yopocho/ChristmasMantelClock/src/ui/ui_font_courier_new_16.c

/*******************************************************************************
 * Size: 16 px
 * Bpp: 1
 * Opts: --bpp 1 --size 16 --no-compress --font ..\..\Downloads\cour.ttf --symbols abcdefghijklmnopqrstuvwxyzABCDEFGHIJKLMNOPQRSTUVWXYZ0123456789:_-+"?!@#$%^&*()[]˅˯ --format lvgl
 ******************************************************************************/

#ifdef __has_include
    #if __has_include("lvgl.h")
        #ifndef LV_LVGL_H_INCLUDE_SIMPLE
            #define LV_LVGL_H_INCLUDE_SIMPLE
        #endif
    #endif
#endif

#ifdef LV_LVGL_H_INCLUDE_SIMPLE
    #include "lvgl.h"
#else
    #include "lvgl.h"
#endif

#ifndef UI_FONT_COURIER_NEW_16
#define UI_FONT_COURIER_NEW_16 1
#endif

#if UI_FONT_COURIER_NEW_16

/*-----------------
 *    BITMAPS
 *----------------*/

/*Store the image of the glyphs*/
static LV_ATTRIBUTE_LARGE_CONST const uint8_t glyph_bitmap[] = {
    /* U+0020 " " */
    0x0,

    /* U+0021 "!" */
    0xaa, 0xa0, 0x30,

    /* U+0022 "\"" */
    0xcb, 0x2c, 0x92,

    /* U+0023 "#" */
    0x28, 0x50, 0xa1, 0x47, 0xe5, 0xa, 0x7f, 0x28,
    0x50, 0xa1, 0x40,

    /* U+0024 "$" */
    0x10, 0x79, 0x92, 0x4, 0x7, 0x1, 0xc1, 0xc6,
    0x78, 0x40, 0x80,

    /* U+0025 "%" */
    0x30, 0x91, 0x21, 0x80, 0x67, 0x13, 0x9, 0x12,
    0x18,

    /* U+0026 "&" */
    0x39, 0x4, 0x10, 0x23, 0x59, 0x62, 0x74,

    /* U+0028 "(" */
    0x29, 0x49, 0x24, 0x89, 0x10,

    /* U+0029 ")" */
    0x89, 0x12, 0x49, 0x29, 0x40,

    /* U+002A "*" */
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
    0x42, 0xe7,

    /* U+0069 "i" */
    0x10, 0x0, 0x3, 0x81, 0x2, 0x4, 0x8, 0x11,
    0xfc,

    /* U+006A "j" */
    0x10, 0x1, 0xf0, 0x84, 0x21, 0x8, 0x42, 0x3f,
    0x0,

    /* U+006B "k" */
    0xc0, 0x40, 0x40, 0x4e, 0x48, 0x50, 0x70, 0x48,
    0x44, 0xc7,

    /* U+006C "l" */
    0x70, 0x20, 0x40, 0x81, 0x2, 0x4, 0x8, 0x11,
    0xfc,

    /* U+006D "m" */
    0xf7, 0x24, 0x92, 0x49, 0x24, 0x92, 0x4b, 0xb6,

    /* U+006E "n" */
    0xdc, 0x62, 0x42, 0x42, 0x42, 0x42, 0xe7,

    /* U+006F "o" */
    0x3c, 0x42, 0x81, 0x81, 0x81, 0x42, 0x3c,

    /* U+0070 "p" */
    0xdc, 0x62, 0x41, 0x41, 0x41, 0x62, 0x5c, 0x40,
    0x40, 0xf0,

    /* U+0071 "q" */
    0x3b, 0x46, 0x82, 0x82, 0x82, 0x46, 0x3a, 0x2,
    0x2, 0xf,

    /* U+0072 "r" */
    0xe6, 0x38, 0x20, 0x20, 0x20, 0x20, 0xfc,

    /* U+0073 "s" */
    0x3c, 0x89, 0x1, 0xe0, 0x30, 0xff, 0x0,

    /* U+0074 "t" */
    0x20, 0x20, 0xfe, 0x20, 0x20, 0x20, 0x20, 0x21,
    0x1e,

    /* U+0075 "u" */
    0xce, 0x42, 0x42, 0x42, 0x42, 0x46, 0x3b,

    /* U+0076 "v" */
    0xf3, 0x90, 0x88, 0x84, 0x41, 0x20, 0xa0, 0x30,

    /* U+0077 "w" */
    0xe3, 0xa0, 0x92, 0x49, 0xa3, 0x51, 0xb0, 0xc8,

    /* U+0078 "x" */
    0xe6, 0x44, 0x28, 0x10, 0x2c, 0x42, 0xe7,

    /* U+0079 "y" */
    0xe3, 0x42, 0x42, 0x24, 0x24, 0x18, 0x8, 0x10,
    0x10, 0xf8,

    /* U+007A "z" */
    0xfe, 0x21, 0x8, 0x41, 0x1f, 0xc0,

    /* U+02C5 "˅" */
    0x81, 0x82, 0x42, 0x44, 0x24, 0x18, 0x18, 0x0,

    /* U+02EF "˯" */
    0xa8
};


/*---------------------
 *  GLYPH DESCRIPTION
 *--------------------*/

static const lv_font_fmt_txt_glyph_dsc_t glyph_dsc[] = {
    {.bitmap_index = 0, .adv_w = 0, .box_w = 0, .box_h = 0, .ofs_x = 0, .ofs_y = 0} /* id = 0 reserved */,
    {.bitmap_index = 0, .adv_w = 154, .box_w = 1, .box_h = 1, .ofs_x = 0, .ofs_y = 0},
    {.bitmap_index = 1, .adv_w = 154, .box_w = 2, .box_h = 10, .ofs_x = 4, .ofs_y = 0},
    {.bitmap_index = 4, .adv_w = 154, .box_w = 6, .box_h = 4, .ofs_x = 2, .ofs_y = 6},
    {.bitmap_index = 7, .adv_w = 154, .box_w = 7, .box_h = 12, .ofs_x = 1, .ofs_y = -1},
    {.bitmap_index = 18, .adv_w = 154, .box_w = 7, .box_h = 12, .ofs_x = 1, .ofs_y = -2},
    {.bitmap_index = 29, .adv_w = 154, .box_w = 7, .box_h = 10, .ofs_x = 1, .ofs_y = 0},
    {.bitmap_index = 38, .adv_w = 154, .box_w = 6, .box_h = 9, .ofs_x = 2, .ofs_y = 0},
    {.bitmap_index = 45, .adv_w = 154, .box_w = 3, .box_h = 12, .ofs_x = 5, .ofs_y = -2},
    {.bitmap_index = 50, .adv_w = 154, .box_w = 3, .box_h = 12, .ofs_x = 2, .ofs_y = -2},
    {.bitmap_index = 55, .adv_w = 154, .box_w = 7, .box_h = 6, .ofs_x = 1, .ofs_y = 4},
    {.bitmap_index = 61, .adv_w = 154, .box_w = 7, .box_h = 9, .ofs_x = 1, .ofs_y = 0},
    {.bitmap_index = 69, .adv_w = 154, .box_w = 7, .box_h = 1, .ofs_x = 1, .ofs_y = 4},
    {.bitmap_index = 70, .adv_w = 154, .box_w = 6, .box_h = 10, .ofs_x = 2, .ofs_y = 0},
    {.bitmap_index = 78, .adv_w = 154, .box_w = 7, .box_h = 10, .ofs_x = 1, .ofs_y = 0},
    {.bitmap_index = 87, .adv_w = 154, .box_w = 7, .box_h = 10, .ofs_x = 1, .ofs_y = 0},
    {.bitmap_index = 96, .adv_w = 154, .box_w = 7, .box_h = 10, .ofs_x = 1, .ofs_y = 0},
    {.bitmap_index = 105, .adv_w = 154, .box_w = 7, .box_h = 10, .ofs_x = 1, .ofs_y = 0},
    {.bitmap_index = 114, .adv_w = 154, .box_w = 7, .box_h = 10, .ofs_x = 1, .ofs_y = 0},
    {.bitmap_index = 123, .adv_w = 154, .box_w = 6, .box_h = 10, .ofs_x = 2, .ofs_y = 0},
    {.bitmap_index = 131, .adv_w = 154, .box_w = 7, .box_h = 10, .ofs_x = 1, .ofs_y = 0},
    {.bitmap_index = 140, .adv_w = 154, .box_w = 6, .box_h = 10, .ofs_x = 2, .ofs_y = 0},
    {.bitmap_index = 148, .adv_w = 154, .box_w = 6, .box_h = 10, .ofs_x = 2, .ofs_y = 0},
    {.bitmap_index = 156, .adv_w = 154, .box_w = 2, .box_h = 7, .ofs_x = 4, .ofs_y = 0},
    {.bitmap_index = 158, .adv_w = 154, .box_w = 6, .box_h = 9, .ofs_x = 2, .ofs_y = 0},
    {.bitmap_index = 165, .adv_w = 154, .box_w = 6, .box_h = 11, .ofs_x = 2, .ofs_y = -1},
    {.bitmap_index = 174, .adv_w = 154, .box_w = 10, .box_h = 9, .ofs_x = 0, .ofs_y = 0},
    {.bitmap_index = 186, .adv_w = 154, .box_w = 8, .box_h = 9, .ofs_x = 1, .ofs_y = 0},
    {.bitmap_index = 195, .adv_w = 154, .box_w = 8, .box_h = 9, .ofs_x = 1, .ofs_y = 0},
    {.bitmap_index = 204, .adv_w = 154, .box_w = 8, .box_h = 9, .ofs_x = 1, .ofs_y = 0},
    {.bitmap_index = 213, .adv_w = 154, .box_w = 8, .box_h = 9, .ofs_x = 1, .ofs_y = 0},
    {.bitmap_index = 222, .adv_w = 154, .box_w = 8, .box_h = 9, .ofs_x = 2, .ofs_y = 0},
    {.bitmap_index = 231, .adv_w = 154, .box_w = 9, .box_h = 9, .ofs_x = 1, .ofs_y = 0},
    {.bitmap_index = 242, .adv_w = 154, .box_w = 8, .box_h = 9, .ofs_x = 1, .ofs_y = 0},
    {.bitmap_index = 251, .adv_w = 154, .box_w = 7, .box_h = 9, .ofs_x = 1, .ofs_y = 0},
    {.bitmap_index = 259, .adv_w = 154, .box_w = 8, .box_h = 9, .ofs_x = 1, .ofs_y = 0},
    {.bitmap_index = 268, .adv_w = 154, .box_w = 9, .box_h = 9, .ofs_x = 1, .ofs_y = 0},
    {.bitmap_index = 279, .adv_w = 154, .box_w = 8, .box_h = 9, .ofs_x = 1, .ofs_y = 0},
    {.bitmap_index = 288, .adv_w = 154, .box_w = 10, .box_h = 9, .ofs_x = 0, .ofs_y = 0},
    {.bitmap_index = 300, .adv_w = 154, .box_w = 9, .box_h = 9, .ofs_x = 1, .ofs_y = 0},
    {.bitmap_index = 311, .adv_w = 154, .box_w = 8, .box_h = 9, .ofs_x = 1, .ofs_y = 0},
    {.bitmap_index = 320, .adv_w = 154, .box_w = 7, .box_h = 9, .ofs_x = 2, .ofs_y = 0},
    {.bitmap_index = 328, .adv_w = 154, .box_w = 8, .box_h = 11, .ofs_x = 1, .ofs_y = -2},
    {.bitmap_index = 339, .adv_w = 154, .box_w = 8, .box_h = 9, .ofs_x = 1, .ofs_y = 0},
    {.bitmap_index = 348, .adv_w = 154, .box_w = 7, .box_h = 9, .ofs_x = 1, .ofs_y = 0},
    {.bitmap_index = 356, .adv_w = 154, .box_w = 7, .box_h = 9, .ofs_x = 1, .ofs_y = 0},
    {.bitmap_index = 364, .adv_w = 154, .box_w = 9, .box_h = 9, .ofs_x = 1, .ofs_y = 0},
    {.bitmap_index = 375, .adv_w = 154, .box_w = 9, .box_h = 9, .ofs_x = 0, .ofs_y = 0},
    {.bitmap_index = 386, .adv_w = 154, .box_w = 9, .box_h = 9, .ofs_x = 0, .ofs_y = 0},
    {.bitmap_index = 397, .adv_w = 154, .box_w = 8, .box_h = 9, .ofs_x = 1, .ofs_y = 0},
    {.bitmap_index = 406, .adv_w = 154, .box_w = 9, .box_h = 9, .ofs_x = 0, .ofs_y = 0},
    {.bitmap_index = 417, .adv_w = 154, .box_w = 7, .box_h = 9, .ofs_x = 1, .ofs_y = 0},
    {.bitmap_index = 425, .adv_w = 154, .box_w = 3, .box_h = 12, .ofs_x = 4, .ofs_y = -2},
    {.bitmap_index = 430, .adv_w = 154, .box_w = 3, .box_h = 12, .ofs_x = 2, .ofs_y = -2},
    {.bitmap_index = 435, .adv_w = 154, .box_w = 6, .box_h = 4, .ofs_x = 2, .ofs_y = 6},
    {.bitmap_index = 438, .adv_w = 154, .box_w = 10, .box_h = 1, .ofs_x = 0, .ofs_y = -5},
    {.bitmap_index = 440, .adv_w = 154, .box_w = 7, .box_h = 7, .ofs_x = 1, .ofs_y = 0},
    {.bitmap_index = 447, .adv_w = 154, .box_w = 8, .box_h = 10, .ofs_x = 1, .ofs_y = 0},
    {.bitmap_index = 457, .adv_w = 154, .box_w = 8, .box_h = 7, .ofs_x = 1, .ofs_y = 0},
    {.bitmap_index = 464, .adv_w = 154, .box_w = 8, .box_h = 10, .ofs_x = 1, .ofs_y = 0},
    {.bitmap_index = 474, .adv_w = 154, .box_w = 8, .box_h = 7, .ofs_x = 1, .ofs_y = 0},
    {.bitmap_index = 481, .adv_w = 154, .box_w = 7, .box_h = 10, .ofs_x = 2, .ofs_y = 0},
    {.bitmap_index = 490, .adv_w = 154, .box_w = 8, .box_h = 10, .ofs_x = 1, .ofs_y = -3},
    {.bitmap_index = 500, .adv_w = 154, .box_w = 8, .box_h = 10, .ofs_x = 1, .ofs_y = 0},
    {.bitmap_index = 510, .adv_w = 154, .box_w = 7, .box_h = 10, .ofs_x = 1, .ofs_y = 0},
    {.bitmap_index = 519, .adv_w = 154, .box_w = 5, .box_h = 13, .ofs_x = 2, .ofs_y = -3},
    {.bitmap_index = 528, .adv_w = 154, .box_w = 8, .box_h = 10, .ofs_x = 2, .ofs_y = 0},
    {.bitmap_index = 538, .adv_w = 154, .box_w = 7, .box_h = 10, .ofs_x = 1, .ofs_y = 0},
    {.bitmap_index = 547, .adv_w = 154, .box_w = 9, .box_h = 7, .ofs_x = 0, .ofs_y = 0},
    {.bitmap_index = 555, .adv_w = 154, .box_w = 8, .box_h = 7, .ofs_x = 1, .ofs_y = 0},
    {.bitmap_index = 562, .adv_w = 154, .box_w = 8, .box_h = 7, .ofs_x = 1, .ofs_y = 0},
    {.bitmap_index = 569, .adv_w = 154, .box_w = 8, .box_h = 10, .ofs_x = 1, .ofs_y = -3},
    {.bitmap_index = 579, .adv_w = 154, .box_w = 8, .box_h = 10, .ofs_x = 1, .ofs_y = -3},
    {.bitmap_index = 589, .adv_w = 154, .box_w = 8, .box_h = 7, .ofs_x = 1, .ofs_y = 0},
    {.bitmap_index = 596, .adv_w = 154, .box_w = 7, .box_h = 7, .ofs_x = 1, .ofs_y = 0},
    {.bitmap_index = 603, .adv_w = 154, .box_w = 8, .box_h = 9, .ofs_x = 1, .ofs_y = 0},
    {.bitmap_index = 612, .adv_w = 154, .box_w = 8, .box_h = 7, .ofs_x = 1, .ofs_y = 0},
    {.bitmap_index = 619, .adv_w = 154, .box_w = 9, .box_h = 7, .ofs_x = 0, .ofs_y = 0},
    {.bitmap_index = 627, .adv_w = 154, .box_w = 9, .box_h = 7, .ofs_x = 0, .ofs_y = 0},
    {.bitmap_index = 635, .adv_w = 154, .box_w = 8, .box_h = 7, .ofs_x = 1, .ofs_y = 0},
    {.bitmap_index = 642, .adv_w = 154, .box_w = 8, .box_h = 10, .ofs_x = 1, .ofs_y = -3},
    {.bitmap_index = 652, .adv_w = 154, .box_w = 6, .box_h = 7, .ofs_x = 2, .ofs_y = 0},
    {.bitmap_index = 658, .adv_w = 154, .box_w = 8, .box_h = 8, .ofs_x = 1, .ofs_y = 0},
    {.bitmap_index = 666, .adv_w = 154, .box_w = 3, .box_h = 2, .ofs_x = 3, .ofs_y = -3}
};

/*---------------------
 *  CHARACTER MAPPING
 *--------------------*/

static const uint8_t glyph_id_ofs_list_0[] = {
    0, 1, 2, 3, 4, 5, 6, 0,
    7, 8, 9, 10, 0, 11, 0, 0,
    12, 13, 14, 15, 16, 17, 18, 19,
    20, 21, 22
};

static const uint16_t unicode_list_4[] = {
    0x0, 0x2a
};

/*Collect the unicode lists and glyph_id offsets*/
static const lv_font_fmt_txt_cmap_t cmaps[] =
{
    {
        .range_start = 32, .range_length = 27, .glyph_id_start = 1,
        .unicode_list = NULL, .glyph_id_ofs_list = glyph_id_ofs_list_0, .list_length = 27, .type = LV_FONT_FMT_TXT_CMAP_FORMAT0_FULL
    },
    {
        .range_start = 63, .range_length = 29, .glyph_id_start = 24,
        .unicode_list = NULL, .glyph_id_ofs_list = NULL, .list_length = 0, .type = LV_FONT_FMT_TXT_CMAP_FORMAT0_TINY
    },
    {
        .range_start = 93, .range_length = 3, .glyph_id_start = 53,
        .unicode_list = NULL, .glyph_id_ofs_list = NULL, .list_length = 0, .type = LV_FONT_FMT_TXT_CMAP_FORMAT0_TINY
    },
    {
        .range_start = 97, .range_length = 26, .glyph_id_start = 56,
        .unicode_list = NULL, .glyph_id_ofs_list = NULL, .list_length = 0, .type = LV_FONT_FMT_TXT_CMAP_FORMAT0_TINY
    },
    {
        .range_start = 709, .range_length = 43, .glyph_id_start = 82,
        .unicode_list = unicode_list_4, .glyph_id_ofs_list = NULL, .list_length = 2, .type = LV_FONT_FMT_TXT_CMAP_SPARSE_TINY
    }
};



/*--------------------
 *  ALL CUSTOM DATA
 *--------------------*/

#if LVGL_VERSION_MAJOR == 8
/*Store all the custom data of the font*/
static  lv_font_fmt_txt_glyph_cache_t cache;
#endif

#if LVGL_VERSION_MAJOR >= 8
static const lv_font_fmt_txt_dsc_t font_dsc = {
#else
static lv_font_fmt_txt_dsc_t font_dsc = {
#endif
    .glyph_bitmap = glyph_bitmap,
    .glyph_dsc = glyph_dsc,
    .cmaps = cmaps,
    .kern_dsc = NULL,
    .kern_scale = 0,
    .cmap_num = 5,
    .bpp = 1,
    .kern_classes = 0,
    .bitmap_format = 0,
#if LVGL_VERSION_MAJOR == 8
    .cache = &cache
#endif
};



/*-----------------
 *  PUBLIC FONT
 *----------------*/

/*Initialize a public general font descriptor*/
#if LVGL_VERSION_MAJOR >= 8
const lv_font_t ui_font_courier_new_16 = {
#else
lv_font_t ui_font_courier_new_16 = {
#endif
    .get_glyph_dsc = lv_font_get_glyph_dsc_fmt_txt,    /*Function pointer to get glyph's data*/
    .get_glyph_bitmap = lv_font_get_bitmap_fmt_txt,    /*Function pointer to get glyph's bitmap*/
    .line_height = 16,          /*The maximum line height required by the font*/
    .base_line = 5,             /*Baseline measured from the bottom of the line*/
#if !(LVGL_VERSION_MAJOR == 6 && LVGL_VERSION_MINOR == 0)
    .subpx = LV_FONT_SUBPX_NONE,
#endif
#if LV_VERSION_CHECK(7, 4, 0) || LVGL_VERSION_MAJOR >= 8
    .underline_position = -4,
    .underline_thickness = 1,
#endif
    .dsc = &font_dsc,          /*The custom font data. Will be accessed by `get_glyph_bitmap/dsc` */
#if LV_VERSION_CHECK(8, 2, 0) || LVGL_VERSION_MAJOR >= 9
    .fallback = NULL,
#endif
    .user_data = NULL,
};



#endif /*#if UI_FONT_COURIER_NEW_16*/
