yopocho/ChristmasMantelClock/src/ui/ui_font_courier_new_20.c

/*******************************************************************************
 * Size: 20 px
 * Bpp: 1
 * Opts: --bpp 1 --size 20 --no-compress --font ..\..\Downloads\cour.ttf --symbols abcdefghijklmnopqrstuvwxyzABCDEFGHIJKLMNOPQRSTUVWXYZ0123456789:_-+"?!@#$%^&*()[]˅˯ --format lvgl
 ******************************************************************************/

#ifdef __has_include
    #if __has_include("lvgl.h")
        #ifndef LV_LVGL_H_INCLUDE_SIMPLE
            #define LV_LVGL_H_INCLUDE_SIMPLE
        #endif
    #endif
#endif

#ifdef LV_LVGL_H_INCLUDE_SIMPLE
    #include "lvgl.h"
#else
    #include "lvgl.h"
#endif

#ifndef UI_FONT_COURIER_NEW_20
#define UI_FONT_COURIER_NEW_20 1
#endif

#if UI_FONT_COURIER_NEW_20

/*-----------------
 *    BITMAPS
 *----------------*/

/*Store the image of the glyphs*/
static LV_ATTRIBUTE_LARGE_CONST const uint8_t glyph_bitmap[] = {
    /* U+0020 " " */
    0x0,

    /* U+0021 "!" */
    0x55, 0x55, 0x3, 0xc0,

    /* U+0022 "\"" */
    0xcf, 0x3c, 0xf3, 0x84,

    /* U+0023 "#" */
    0x14, 0x14, 0x14, 0x14, 0x14, 0xff, 0x34, 0x34,
    0x24, 0xff, 0x24, 0x24, 0x24, 0x24, 0x24,

    /* U+0024 "$" */
    0x8, 0x8, 0x36, 0x42, 0x40, 0x60, 0x3c, 0x3,
    0x1, 0x81, 0xc3, 0xbe, 0x8, 0x8, 0x8, 0x8,

    /* U+0025 "%" */
    0x70, 0x88, 0x88, 0x88, 0x70, 0x1, 0xe, 0x70,
    0x9e, 0x33, 0x21, 0x33, 0x1e,

    /* U+0026 "&" */
    0x3c, 0xc1, 0x2, 0x2, 0xe, 0x64, 0xc6, 0x8d,
    0x99, 0xc8,

    /* U+0028 "(" */
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
    0x20, 0x10, 0x8, 0x1f, 0xe2, 0x1, 0x0, 0x80,
    0x40, 0x20, 0x10, 0xc, 0x23, 0xe0,

    /* U+0075 "u" */
    0xe3, 0x88, 0x22, 0x8, 0x82, 0x20, 0x88, 0x22,
    0x8, 0x86, 0x1e, 0xc0,

    /* U+0076 "v" */
    0xf3, 0xd0, 0x24, 0x10, 0x84, 0x21, 0x4, 0x81,
    0x20, 0x30, 0xc, 0x0,

    /* U+0077 "w" */
    0xe1, 0xe0, 0x24, 0xc9, 0x32, 0x4c, 0x94, 0xa5,
    0x30, 0xcc, 0x21, 0x0,

    /* U+0078 "x" */
    0xf3, 0xc8, 0x41, 0x20, 0x30, 0xc, 0x4, 0x82,
    0x11, 0x2, 0xf3, 0xc0,

    /* U+0079 "y" */
    0xf1, 0xd0, 0x22, 0x8, 0x82, 0x11, 0x4, 0x40,
    0xa0, 0x28, 0x4, 0x1, 0x0, 0x80, 0x20, 0xfc,
    0x0,

    /* U+007A "z" */
    0xff, 0xa, 0x20, 0x41, 0x4, 0x10, 0xe1, 0xfe,

    /* U+02C5 "˅" */
    0x80, 0x50, 0x14, 0x8, 0x82, 0x21, 0x4, 0x41,
    0x20, 0x28, 0x4, 0x0, 0x0,

    /* U+02EF "˯" */
    0x96, 0x0
};


/*---------------------
 *  GLYPH DESCRIPTION
 *--------------------*/

static const lv_font_fmt_txt_glyph_dsc_t glyph_dsc[] = {
    {.bitmap_index = 0, .adv_w = 0, .box_w = 0, .box_h = 0, .ofs_x = 0, .ofs_y = 0} /* id = 0 reserved */,
    {.bitmap_index = 0, .adv_w = 192, .box_w = 1, .box_h = 1, .ofs_x = 0, .ofs_y = 0},
    {.bitmap_index = 1, .adv_w = 192, .box_w = 2, .box_h = 13, .ofs_x = 5, .ofs_y = 0},
    {.bitmap_index = 5, .adv_w = 192, .box_w = 6, .box_h = 5, .ofs_x = 3, .ofs_y = 8},
    {.bitmap_index = 9, .adv_w = 192, .box_w = 8, .box_h = 15, .ofs_x = 2, .ofs_y = -1},
    {.bitmap_index = 24, .adv_w = 192, .box_w = 8, .box_h = 16, .ofs_x = 2, .ofs_y = -2},
    {.bitmap_index = 40, .adv_w = 192, .box_w = 8, .box_h = 13, .ofs_x = 2, .ofs_y = 0},
    {.bitmap_index = 53, .adv_w = 192, .box_w = 7, .box_h = 11, .ofs_x = 2, .ofs_y = 0},
    {.bitmap_index = 63, .adv_w = 192, .box_w = 3, .box_h = 15, .ofs_x = 6, .ofs_y = -2},
    {.bitmap_index = 69, .adv_w = 192, .box_w = 3, .box_h = 15, .ofs_x = 3, .ofs_y = -2},
    {.bitmap_index = 75, .adv_w = 192, .box_w = 7, .box_h = 8, .ofs_x = 3, .ofs_y = 5},
    {.bitmap_index = 82, .adv_w = 192, .box_w = 9, .box_h = 11, .ofs_x = 2, .ofs_y = 0},
    {.bitmap_index = 95, .adv_w = 192, .box_w = 8, .box_h = 1, .ofs_x = 2, .ofs_y = 5},
    {.bitmap_index = 96, .adv_w = 192, .box_w = 8, .box_h = 13, .ofs_x = 2, .ofs_y = 0},
    {.bitmap_index = 109, .adv_w = 192, .box_w = 7, .box_h = 13, .ofs_x = 3, .ofs_y = 0},
    {.bitmap_index = 121, .adv_w = 192, .box_w = 8, .box_h = 13, .ofs_x = 2, .ofs_y = 0},
    {.bitmap_index = 134, .adv_w = 192, .box_w = 8, .box_h = 13, .ofs_x = 2, .ofs_y = 0},
    {.bitmap_index = 147, .adv_w = 192, .box_w = 8, .box_h = 13, .ofs_x = 2, .ofs_y = 0},
    {.bitmap_index = 160, .adv_w = 192, .box_w = 8, .box_h = 13, .ofs_x = 2, .ofs_y = 0},
    {.bitmap_index = 173, .adv_w = 192, .box_w = 8, .box_h = 13, .ofs_x = 3, .ofs_y = 0},
    {.bitmap_index = 186, .adv_w = 192, .box_w = 8, .box_h = 13, .ofs_x = 2, .ofs_y = 0},
    {.bitmap_index = 199, .adv_w = 192, .box_w = 8, .box_h = 13, .ofs_x = 2, .ofs_y = 0},
    {.bitmap_index = 212, .adv_w = 192, .box_w = 8, .box_h = 13, .ofs_x = 3, .ofs_y = 0},
    {.bitmap_index = 225, .adv_w = 192, .box_w = 3, .box_h = 9, .ofs_x = 4, .ofs_y = 0},
    {.bitmap_index = 229, .adv_w = 192, .box_w = 7, .box_h = 12, .ofs_x = 3, .ofs_y = 0},
    {.bitmap_index = 240, .adv_w = 192, .box_w = 7, .box_h = 14, .ofs_x = 2, .ofs_y = -1},
    {.bitmap_index = 253, .adv_w = 192, .box_w = 12, .box_h = 12, .ofs_x = 0, .ofs_y = 0},
    {.bitmap_index = 271, .adv_w = 192, .box_w = 10, .box_h = 12, .ofs_x = 0, .ofs_y = 0},
    {.bitmap_index = 286, .adv_w = 192, .box_w = 9, .box_h = 12, .ofs_x = 1, .ofs_y = 0},
    {.bitmap_index = 300, .adv_w = 192, .box_w = 9, .box_h = 12, .ofs_x = 2, .ofs_y = 0},
    {.bitmap_index = 314, .adv_w = 192, .box_w = 10, .box_h = 12, .ofs_x = 1, .ofs_y = 0},
    {.bitmap_index = 329, .adv_w = 192, .box_w = 10, .box_h = 12, .ofs_x = 1, .ofs_y = 0},
    {.bitmap_index = 344, .adv_w = 192, .box_w = 10, .box_h = 12, .ofs_x = 1, .ofs_y = 0},
    {.bitmap_index = 359, .adv_w = 192, .box_w = 9, .box_h = 12, .ofs_x = 2, .ofs_y = 0},
    {.bitmap_index = 373, .adv_w = 192, .box_w = 7, .box_h = 12, .ofs_x = 3, .ofs_y = 0},
    {.bitmap_index = 384, .adv_w = 192, .box_w = 11, .box_h = 12, .ofs_x = 2, .ofs_y = 0},
    {.bitmap_index = 401, .adv_w = 192, .box_w = 11, .box_h = 12, .ofs_x = 1, .ofs_y = 0},
    {.bitmap_index = 418, .adv_w = 192, .box_w = 10, .box_h = 12, .ofs_x = 1, .ofs_y = 0},
    {.bitmap_index = 433, .adv_w = 192, .box_w = 11, .box_h = 12, .ofs_x = 0, .ofs_y = 0},
    {.bitmap_index = 450, .adv_w = 192, .box_w = 11, .box_h = 12, .ofs_x = 0, .ofs_y = 0},
    {.bitmap_index = 467, .adv_w = 192, .box_w = 10, .box_h = 12, .ofs_x = 1, .ofs_y = 0},
    {.bitmap_index = 482, .adv_w = 192, .box_w = 10, .box_h = 12, .ofs_x = 1, .ofs_y = 0},
    {.bitmap_index = 497, .adv_w = 192, .box_w = 10, .box_h = 14, .ofs_x = 1, .ofs_y = -2},
    {.bitmap_index = 515, .adv_w = 192, .box_w = 12, .box_h = 12, .ofs_x = 1, .ofs_y = 0},
    {.bitmap_index = 533, .adv_w = 192, .box_w = 8, .box_h = 12, .ofs_x = 2, .ofs_y = 0},
    {.bitmap_index = 545, .adv_w = 192, .box_w = 9, .box_h = 12, .ofs_x = 1, .ofs_y = 0},
    {.bitmap_index = 559, .adv_w = 192, .box_w = 10, .box_h = 12, .ofs_x = 1, .ofs_y = 0},
    {.bitmap_index = 574, .adv_w = 192, .box_w = 12, .box_h = 12, .ofs_x = 0, .ofs_y = 0},
    {.bitmap_index = 592, .adv_w = 192, .box_w = 12, .box_h = 12, .ofs_x = 0, .ofs_y = 0},
    {.bitmap_index = 610, .adv_w = 192, .box_w = 10, .box_h = 12, .ofs_x = 1, .ofs_y = 0},
    {.bitmap_index = 625, .adv_w = 192, .box_w = 11, .box_h = 12, .ofs_x = 1, .ofs_y = 0},
    {.bitmap_index = 642, .adv_w = 192, .box_w = 9, .box_h = 12, .ofs_x = 2, .ofs_y = 0},
    {.bitmap_index = 656, .adv_w = 192, .box_w = 4, .box_h = 15, .ofs_x = 6, .ofs_y = -2},
    {.bitmap_index = 664, .adv_w = 192, .box_w = 4, .box_h = 15, .ofs_x = 3, .ofs_y = -2},
    {.bitmap_index = 672, .adv_w = 192, .box_w = 8, .box_h = 5, .ofs_x = 2, .ofs_y = 7},
    {.bitmap_index = 677, .adv_w = 192, .box_w = 12, .box_h = 1, .ofs_x = 0, .ofs_y = -6},
    {.bitmap_index = 679, .adv_w = 192, .box_w = 10, .box_h = 9, .ofs_x = 1, .ofs_y = 0},
    {.bitmap_index = 691, .adv_w = 192, .box_w = 11, .box_h = 13, .ofs_x = 0, .ofs_y = 0},
    {.bitmap_index = 709, .adv_w = 192, .box_w = 9, .box_h = 9, .ofs_x = 2, .ofs_y = 0},
    {.bitmap_index = 720, .adv_w = 192, .box_w = 11, .box_h = 13, .ofs_x = 1, .ofs_y = 0},
    {.bitmap_index = 738, .adv_w = 192, .box_w = 9, .box_h = 9, .ofs_x = 1, .ofs_y = 0},
    {.bitmap_index = 749, .adv_w = 192, .box_w = 9, .box_h = 13, .ofs_x = 2, .ofs_y = 0},
    {.bitmap_index = 764, .adv_w = 192, .box_w = 10, .box_h = 13, .ofs_x = 1, .ofs_y = -4},
    {.bitmap_index = 781, .adv_w = 192, .box_w = 10, .box_h = 13, .ofs_x = 0, .ofs_y = 0},
    {.bitmap_index = 798, .adv_w = 192, .box_w = 9, .box_h = 13, .ofs_x = 1, .ofs_y = 0},
    {.bitmap_index = 813, .adv_w = 192, .box_w = 6, .box_h = 17, .ofs_x = 2, .ofs_y = -4},
    {.bitmap_index = 826, .adv_w = 192, .box_w = 10, .box_h = 13, .ofs_x = 2, .ofs_y = 0},
    {.bitmap_index = 843, .adv_w = 192, .box_w = 9, .box_h = 13, .ofs_x = 2, .ofs_y = 0},
    {.bitmap_index = 858, .adv_w = 192, .box_w = 11, .box_h = 9, .ofs_x = 0, .ofs_y = 0},
    {.bitmap_index = 871, .adv_w = 192, .box_w = 9, .box_h = 9, .ofs_x = 2, .ofs_y = 0},
    {.bitmap_index = 882, .adv_w = 192, .box_w = 9, .box_h = 9, .ofs_x = 1, .ofs_y = 0},
    {.bitmap_index = 893, .adv_w = 192, .box_w = 11, .box_h = 13, .ofs_x = 0, .ofs_y = -4},
    {.bitmap_index = 911, .adv_w = 192, .box_w = 11, .box_h = 13, .ofs_x = 1, .ofs_y = -4},
    {.bitmap_index = 929, .adv_w = 192, .box_w = 10, .box_h = 9, .ofs_x = 1, .ofs_y = 0},
    {.bitmap_index = 941, .adv_w = 192, .box_w = 9, .box_h = 9, .ofs_x = 2, .ofs_y = 0},
    {.bitmap_index = 952, .adv_w = 192, .box_w = 9, .box_h = 12, .ofs_x = 1, .ofs_y = 0},
    {.bitmap_index = 966, .adv_w = 192, .box_w = 10, .box_h = 9, .ofs_x = 1, .ofs_y = 0},
    {.bitmap_index = 978, .adv_w = 192, .box_w = 10, .box_h = 9, .ofs_x = 1, .ofs_y = 0},
    {.bitmap_index = 990, .adv_w = 192, .box_w = 10, .box_h = 9, .ofs_x = 1, .ofs_y = 0},
    {.bitmap_index = 1002, .adv_w = 192, .box_w = 10, .box_h = 9, .ofs_x = 1, .ofs_y = 0},
    {.bitmap_index = 1014, .adv_w = 192, .box_w = 10, .box_h = 13, .ofs_x = 1, .ofs_y = -4},
    {.bitmap_index = 1031, .adv_w = 192, .box_w = 7, .box_h = 9, .ofs_x = 2, .ofs_y = 0},
    {.bitmap_index = 1039, .adv_w = 192, .box_w = 10, .box_h = 10, .ofs_x = 1, .ofs_y = 1},
    {.bitmap_index = 1052, .adv_w = 192, .box_w = 4, .box_h = 3, .ofs_x = 4, .ofs_y = -4}
};

/*---------------------
 *  CHARACTER MAPPING
 *--------------------*/

static const uint8_t glyph_id_ofs_list_0[] = {
    0, 1, 2, 3, 4, 5, 6, 0,
    7, 8, 9, 10, 0, 11, 0, 0,
    12, 13, 14, 15, 16, 17, 18, 19,
    20, 21, 22
};

static const uint16_t unicode_list_4[] = {
    0x0, 0x2a
};

/*Collect the unicode lists and glyph_id offsets*/
static const lv_font_fmt_txt_cmap_t cmaps[] =
{
    {
        .range_start = 32, .range_length = 27, .glyph_id_start = 1,
        .unicode_list = NULL, .glyph_id_ofs_list = glyph_id_ofs_list_0, .list_length = 27, .type = LV_FONT_FMT_TXT_CMAP_FORMAT0_FULL
    },
    {
        .range_start = 63, .range_length = 29, .glyph_id_start = 24,
        .unicode_list = NULL, .glyph_id_ofs_list = NULL, .list_length = 0, .type = LV_FONT_FMT_TXT_CMAP_FORMAT0_TINY
    },
    {
        .range_start = 93, .range_length = 3, .glyph_id_start = 53,
        .unicode_list = NULL, .glyph_id_ofs_list = NULL, .list_length = 0, .type = LV_FONT_FMT_TXT_CMAP_FORMAT0_TINY
    },
    {
        .range_start = 97, .range_length = 26, .glyph_id_start = 56,
        .unicode_list = NULL, .glyph_id_ofs_list = NULL, .list_length = 0, .type = LV_FONT_FMT_TXT_CMAP_FORMAT0_TINY
    },
    {
        .range_start = 709, .range_length = 43, .glyph_id_start = 82,
        .unicode_list = unicode_list_4, .glyph_id_ofs_list = NULL, .list_length = 2, .type = LV_FONT_FMT_TXT_CMAP_SPARSE_TINY
    }
};



/*--------------------
 *  ALL CUSTOM DATA
 *--------------------*/

#if LVGL_VERSION_MAJOR == 8
/*Store all the custom data of the font*/
static  lv_font_fmt_txt_glyph_cache_t cache;
#endif

#if LVGL_VERSION_MAJOR >= 8
static const lv_font_fmt_txt_dsc_t font_dsc = {
#else
static lv_font_fmt_txt_dsc_t font_dsc = {
#endif
    .glyph_bitmap = glyph_bitmap,
    .glyph_dsc = glyph_dsc,
    .cmaps = cmaps,
    .kern_dsc = NULL,
    .kern_scale = 0,
    .cmap_num = 5,
    .bpp = 1,
    .kern_classes = 0,
    .bitmap_format = 0,
#if LVGL_VERSION_MAJOR == 8
    .cache = &cache
#endif
};



/*-----------------
 *  PUBLIC FONT
 *----------------*/

/*Initialize a public general font descriptor*/
#if LVGL_VERSION_MAJOR >= 8
const lv_font_t ui_font_courier_new_20 = {
#else
lv_font_t ui_font_courier_new_20 = {
#endif
    .get_glyph_dsc = lv_font_get_glyph_dsc_fmt_txt,    /*Function pointer to get glyph's data*/
    .get_glyph_bitmap = lv_font_get_bitmap_fmt_txt,    /*Function pointer to get glyph's bitmap*/
    .line_height = 20,          /*The maximum line height required by the font*/
    .base_line = 6,             /*Baseline measured from the bottom of the line*/
#if !(LVGL_VERSION_MAJOR == 6 && LVGL_VERSION_MINOR == 0)
    .subpx = LV_FONT_SUBPX_NONE,
#endif
#if LV_VERSION_CHECK(7, 4, 0) || LVGL_VERSION_MAJOR >= 8
    .underline_position = -5,
    .underline_thickness = 1,
#endif
    .dsc = &font_dsc,          /*The custom font data. Will be accessed by `get_glyph_bitmap/dsc` */
#if LV_VERSION_CHECK(8, 2, 0) || LVGL_VERSION_MAJOR >= 9
    .fallback = NULL,
#endif
    .user_data = NULL,
};



#endif /*#if UI_FONT_COURIER_NEW_20*/
