yopocho/ChristmasMantelClock/src/ui/ui_font_courier_new_40.c

/*******************************************************************************
 * Size: 40 px
 * Bpp: 1
 * Opts: --bpp 1 --size 40 --no-compress --font ..\..\Downloads\cour.ttf --symbols abcdefghijklmnopqrstuvwxyzABCDEFGHIJKLMNOPQRSTUVWXYZ0123456789:_-+"?!@#$%^&*()[]˅˯ --format lvgl
 ******************************************************************************/

#ifdef __has_include
    #if __has_include("lvgl.h")
        #ifndef LV_LVGL_H_INCLUDE_SIMPLE
            #define LV_LVGL_H_INCLUDE_SIMPLE
        #endif
    #endif
#endif

#ifdef LV_LVGL_H_INCLUDE_SIMPLE
    #include "lvgl.h"
#else
    #include "lvgl.h"
#endif

#ifndef UI_FONT_COURIER_NEW_40
#define UI_FONT_COURIER_NEW_40 1
#endif

#if UI_FONT_COURIER_NEW_40

/*-----------------
 *    BITMAPS
 *----------------*/

/*Store the image of the glyphs*/
static LV_ATTRIBUTE_LARGE_CONST const uint8_t glyph_bitmap[] = {
    /* U+0020 " " */
    0x0,

    /* U+0021 "!" */
    0x63, 0x18, 0xc6, 0x31, 0x8c, 0x63, 0x18, 0xc6,
    0x31, 0x8c, 0x60, 0x0, 0x0, 0x0, 0x9f, 0xff,
    0xc8,

    /* U+0022 "\"" */
    0xf8, 0x7f, 0xe1, 0xf7, 0x87, 0x9e, 0x1e, 0x78,
    0x79, 0xe1, 0xe7, 0x3, 0x9c, 0xe, 0x70, 0x38,
    0xc0, 0xc3, 0x3, 0x0,

    /* U+0023 "#" */
    0x0, 0x0, 0x3, 0xc, 0x1, 0x86, 0x0, 0xc3,
    0x0, 0x61, 0x80, 0x30, 0xc0, 0x18, 0x60, 0xc,
    0x30, 0x6, 0x18, 0x3, 0xc, 0x1, 0x86, 0xf,
    0xff, 0xf0, 0xe3, 0x0, 0x71, 0x80, 0x38, 0xc0,
    0x18, 0x60, 0xc, 0x30, 0x6, 0x18, 0x3f, 0xff,
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
    0x20, 0x6, 0x6, 0x0, 0x20, 0x40, 0x3, 0xc,
    0x0, 0x19, 0x80, 0x1, 0x98, 0x0, 0xf, 0x0,
    0x0, 0xf0, 0x0, 0x6, 0x0, 0x0, 0x60, 0x0,
    0x0, 0x0,

    /* U+02EF "˯" */
    0xc3, 0xe7, 0x7e, 0x3c, 0x18
};


/*---------------------
 *  GLYPH DESCRIPTION
 *--------------------*/

static const lv_font_fmt_txt_glyph_dsc_t glyph_dsc[] = {
    {.bitmap_index = 0, .adv_w = 0, .box_w = 0, .box_h = 0, .ofs_x = 0, .ofs_y = 0} /* id = 0 reserved */,
    {.bitmap_index = 0, .adv_w = 384, .box_w = 1, .box_h = 1, .ofs_x = 0, .ofs_y = 0},
    {.bitmap_index = 1, .adv_w = 384, .box_w = 5, .box_h = 27, .ofs_x = 10, .ofs_y = -1},
    {.bitmap_index = 18, .adv_w = 384, .box_w = 14, .box_h = 11, .ofs_x = 5, .ofs_y = 14},
    {.bitmap_index = 38, .adv_w = 384, .box_w = 17, .box_h = 29, .ofs_x = 4, .ofs_y = -2},
    {.bitmap_index = 100, .adv_w = 384, .box_w = 15, .box_h = 32, .ofs_x = 4, .ofs_y = -4},
    {.bitmap_index = 160, .adv_w = 384, .box_w = 16, .box_h = 26, .ofs_x = 3, .ofs_y = -1},
    {.bitmap_index = 212, .adv_w = 384, .box_w = 15, .box_h = 22, .ofs_x = 5, .ofs_y = -1},
    {.bitmap_index = 254, .adv_w = 384, .box_w = 6, .box_h = 31, .ofs_x = 12, .ofs_y = -6},
    {.bitmap_index = 278, .adv_w = 384, .box_w = 6, .box_h = 31, .ofs_x = 6, .ofs_y = -6},
    {.bitmap_index = 302, .adv_w = 384, .box_w = 16, .box_h = 15, .ofs_x = 4, .ofs_y = 10},
    {.bitmap_index = 332, .adv_w = 384, .box_w = 19, .box_h = 21, .ofs_x = 2, .ofs_y = 1},
    {.bitmap_index = 382, .adv_w = 384, .box_w = 17, .box_h = 1, .ofs_x = 4, .ofs_y = 11},
    {.bitmap_index = 385, .adv_w = 384, .box_w = 15, .box_h = 27, .ofs_x = 4, .ofs_y = -1},
    {.bitmap_index = 436, .adv_w = 384, .box_w = 15, .box_h = 26, .ofs_x = 4, .ofs_y = 0},
    {.bitmap_index = 485, .adv_w = 384, .box_w = 16, .box_h = 25, .ofs_x = 3, .ofs_y = 0},
    {.bitmap_index = 535, .adv_w = 384, .box_w = 17, .box_h = 27, .ofs_x = 3, .ofs_y = -1},
    {.bitmap_index = 593, .adv_w = 384, .box_w = 15, .box_h = 25, .ofs_x = 4, .ofs_y = 0},
    {.bitmap_index = 640, .adv_w = 384, .box_w = 16, .box_h = 26, .ofs_x = 4, .ofs_y = -1},
    {.bitmap_index = 692, .adv_w = 384, .box_w = 15, .box_h = 27, .ofs_x = 5, .ofs_y = -1},
    {.bitmap_index = 743, .adv_w = 384, .box_w = 15, .box_h = 25, .ofs_x = 4, .ofs_y = 0},
    {.bitmap_index = 790, .adv_w = 384, .box_w = 15, .box_h = 27, .ofs_x = 5, .ofs_y = -1},
    {.bitmap_index = 841, .adv_w = 384, .box_w = 15, .box_h = 27, .ofs_x = 5, .ofs_y = -1},
    {.bitmap_index = 892, .adv_w = 384, .box_w = 6, .box_h = 18, .ofs_x = 9, .ofs_y = -1},
    {.bitmap_index = 906, .adv_w = 384, .box_w = 14, .box_h = 26, .ofs_x = 5, .ofs_y = -1},
    {.bitmap_index = 952, .adv_w = 384, .box_w = 15, .box_h = 28, .ofs_x = 4, .ofs_y = -2},
    {.bitmap_index = 1005, .adv_w = 384, .box_w = 23, .box_h = 24, .ofs_x = 1, .ofs_y = 0},
    {.bitmap_index = 1074, .adv_w = 384, .box_w = 21, .box_h = 24, .ofs_x = 1, .ofs_y = 0},
    {.bitmap_index = 1137, .adv_w = 384, .box_w = 19, .box_h = 26, .ofs_x = 2, .ofs_y = -1},
    {.bitmap_index = 1199, .adv_w = 384, .box_w = 20, .box_h = 24, .ofs_x = 3, .ofs_y = 0},
    {.bitmap_index = 1259, .adv_w = 384, .box_w = 20, .box_h = 24, .ofs_x = 1, .ofs_y = 0},
    {.bitmap_index = 1319, .adv_w = 384, .box_w = 19, .box_h = 24, .ofs_x = 3, .ofs_y = 0},
    {.bitmap_index = 1376, .adv_w = 384, .box_w = 20, .box_h = 26, .ofs_x = 2, .ofs_y = -1},
    {.bitmap_index = 1441, .adv_w = 384, .box_w = 20, .box_h = 24, .ofs_x = 2, .ofs_y = 0},
    {.bitmap_index = 1501, .adv_w = 384, .box_w = 15, .box_h = 24, .ofs_x = 4, .ofs_y = 0},
    {.bitmap_index = 1546, .adv_w = 384, .box_w = 20, .box_h = 25, .ofs_x = 3, .ofs_y = -1},
    {.bitmap_index = 1609, .adv_w = 384, .box_w = 22, .box_h = 24, .ofs_x = 2, .ofs_y = 0},
    {.bitmap_index = 1675, .adv_w = 384, .box_w = 19, .box_h = 24, .ofs_x = 2, .ofs_y = 0},
    {.bitmap_index = 1732, .adv_w = 384, .box_w = 23, .box_h = 24, .ofs_x = 1, .ofs_y = 0},
    {.bitmap_index = 1801, .adv_w = 384, .box_w = 22, .box_h = 24, .ofs_x = 1, .ofs_y = 0},
    {.bitmap_index = 1867, .adv_w = 384, .box_w = 20, .box_h = 26, .ofs_x = 2, .ofs_y = -1},
    {.bitmap_index = 1932, .adv_w = 384, .box_w = 18, .box_h = 24, .ofs_x = 3, .ofs_y = 0},
    {.bitmap_index = 1986, .adv_w = 384, .box_w = 20, .box_h = 29, .ofs_x = 2, .ofs_y = -4},
    {.bitmap_index = 2059, .adv_w = 384, .box_w = 22, .box_h = 24, .ofs_x = 2, .ofs_y = 0},
    {.bitmap_index = 2125, .adv_w = 384, .box_w = 17, .box_h = 26, .ofs_x = 4, .ofs_y = -1},
    {.bitmap_index = 2181, .adv_w = 384, .box_w = 19, .box_h = 24, .ofs_x = 3, .ofs_y = 0},
    {.bitmap_index = 2238, .adv_w = 384, .box_w = 21, .box_h = 25, .ofs_x = 2, .ofs_y = -1},
    {.bitmap_index = 2304, .adv_w = 384, .box_w = 24, .box_h = 24, .ofs_x = 0, .ofs_y = 0},
    {.bitmap_index = 2376, .adv_w = 384, .box_w = 22, .box_h = 24, .ofs_x = 1, .ofs_y = 0},
    {.bitmap_index = 2442, .adv_w = 384, .box_w = 21, .box_h = 24, .ofs_x = 2, .ofs_y = 0},
    {.bitmap_index = 2505, .adv_w = 384, .box_w = 20, .box_h = 24, .ofs_x = 2, .ofs_y = 0},
    {.bitmap_index = 2565, .adv_w = 384, .box_w = 16, .box_h = 24, .ofs_x = 4, .ofs_y = 0},
    {.bitmap_index = 2613, .adv_w = 384, .box_w = 7, .box_h = 29, .ofs_x = 11, .ofs_y = -4},
    {.bitmap_index = 2639, .adv_w = 384, .box_w = 7, .box_h = 29, .ofs_x = 6, .ofs_y = -4},
    {.bitmap_index = 2665, .adv_w = 384, .box_w = 15, .box_h = 11, .ofs_x = 4, .ofs_y = 15},
    {.bitmap_index = 2686, .adv_w = 384, .box_w = 24, .box_h = 1, .ofs_x = 0, .ofs_y = -11},
    {.bitmap_index = 2689, .adv_w = 384, .box_w = 19, .box_h = 19, .ofs_x = 3, .ofs_y = -1},
    {.bitmap_index = 2735, .adv_w = 384, .box_w = 22, .box_h = 26, .ofs_x = 0, .ofs_y = -1},
    {.bitmap_index = 2807, .adv_w = 384, .box_w = 18, .box_h = 19, .ofs_x = 3, .ofs_y = -1},
    {.bitmap_index = 2850, .adv_w = 384, .box_w = 21, .box_h = 26, .ofs_x = 2, .ofs_y = -1},
    {.bitmap_index = 2919, .adv_w = 384, .box_w = 19, .box_h = 19, .ofs_x = 2, .ofs_y = -1},
    {.bitmap_index = 2965, .adv_w = 384, .box_w = 18, .box_h = 25, .ofs_x = 4, .ofs_y = 0},
    {.bitmap_index = 3022, .adv_w = 384, .box_w = 20, .box_h = 26, .ofs_x = 2, .ofs_y = -8},
    {.bitmap_index = 3087, .adv_w = 384, .box_w = 21, .box_h = 25, .ofs_x = 1, .ofs_y = 0},
    {.bitmap_index = 3153, .adv_w = 384, .box_w = 17, .box_h = 26, .ofs_x = 4, .ofs_y = 0},
    {.bitmap_index = 3209, .adv_w = 384, .box_w = 13, .box_h = 34, .ofs_x = 3, .ofs_y = -8},
    {.bitmap_index = 3265, .adv_w = 384, .box_w = 20, .box_h = 25, .ofs_x = 3, .ofs_y = 0},
    {.bitmap_index = 3328, .adv_w = 384, .box_w = 17, .box_h = 25, .ofs_x = 4, .ofs_y = 0},
    {.bitmap_index = 3382, .adv_w = 384, .box_w = 23, .box_h = 18, .ofs_x = 1, .ofs_y = 0},
    {.bitmap_index = 3434, .adv_w = 384, .box_w = 20, .box_h = 18, .ofs_x = 2, .ofs_y = 0},
    {.bitmap_index = 3479, .adv_w = 384, .box_w = 19, .box_h = 19, .ofs_x = 3, .ofs_y = -1},
    {.bitmap_index = 3525, .adv_w = 384, .box_w = 21, .box_h = 26, .ofs_x = 1, .ofs_y = -8},
    {.bitmap_index = 3594, .adv_w = 384, .box_w = 21, .box_h = 26, .ofs_x = 2, .ofs_y = -8},
    {.bitmap_index = 3663, .adv_w = 384, .box_w = 19, .box_h = 18, .ofs_x = 3, .ofs_y = 0},
    {.bitmap_index = 3706, .adv_w = 384, .box_w = 16, .box_h = 19, .ofs_x = 4, .ofs_y = -1},
    {.bitmap_index = 3744, .adv_w = 384, .box_w = 19, .box_h = 25, .ofs_x = 3, .ofs_y = -1},
    {.bitmap_index = 3804, .adv_w = 384, .box_w = 20, .box_h = 18, .ofs_x = 2, .ofs_y = -1},
    {.bitmap_index = 3849, .adv_w = 384, .box_w = 22, .box_h = 17, .ofs_x = 1, .ofs_y = 0},
    {.bitmap_index = 3896, .adv_w = 384, .box_w = 22, .box_h = 17, .ofs_x = 1, .ofs_y = 0},
    {.bitmap_index = 3943, .adv_w = 384, .box_w = 20, .box_h = 17, .ofs_x = 2, .ofs_y = 0},
    {.bitmap_index = 3986, .adv_w = 384, .box_w = 20, .box_h = 25, .ofs_x = 3, .ofs_y = -8},
    {.bitmap_index = 4049, .adv_w = 384, .box_w = 16, .box_h = 17, .ofs_x = 4, .ofs_y = 0},
    {.bitmap_index = 4083, .adv_w = 384, .box_w = 20, .box_h = 20, .ofs_x = 2, .ofs_y = 2},
    {.bitmap_index = 4133, .adv_w = 384, .box_w = 8, .box_h = 5, .ofs_x = 8, .ofs_y = -8}
};

/*---------------------
 *  CHARACTER MAPPING
 *--------------------*/

static const uint8_t glyph_id_ofs_list_0[] = {
    0, 1, 2, 3, 4, 5, 6, 0,
    7, 8, 9, 10, 0, 11, 0, 0,
    12, 13, 14, 15, 16, 17, 18, 19,
    20, 21, 22
};

static const uint16_t unicode_list_4[] = {
    0x0, 0x2a
};

/*Collect the unicode lists and glyph_id offsets*/
static const lv_font_fmt_txt_cmap_t cmaps[] =
{
    {
        .range_start = 32, .range_length = 27, .glyph_id_start = 1,
        .unicode_list = NULL, .glyph_id_ofs_list = glyph_id_ofs_list_0, .list_length = 27, .type = LV_FONT_FMT_TXT_CMAP_FORMAT0_FULL
    },
    {
        .range_start = 63, .range_length = 29, .glyph_id_start = 24,
        .unicode_list = NULL, .glyph_id_ofs_list = NULL, .list_length = 0, .type = LV_FONT_FMT_TXT_CMAP_FORMAT0_TINY
    },
    {
        .range_start = 93, .range_length = 3, .glyph_id_start = 53,
        .unicode_list = NULL, .glyph_id_ofs_list = NULL, .list_length = 0, .type = LV_FONT_FMT_TXT_CMAP_FORMAT0_TINY
    },
    {
        .range_start = 97, .range_length = 26, .glyph_id_start = 56,
        .unicode_list = NULL, .glyph_id_ofs_list = NULL, .list_length = 0, .type = LV_FONT_FMT_TXT_CMAP_FORMAT0_TINY
    },
    {
        .range_start = 709, .range_length = 43, .glyph_id_start = 82,
        .unicode_list = unicode_list_4, .glyph_id_ofs_list = NULL, .list_length = 2, .type = LV_FONT_FMT_TXT_CMAP_SPARSE_TINY
    }
};



/*--------------------
 *  ALL CUSTOM DATA
 *--------------------*/

#if LVGL_VERSION_MAJOR == 8
/*Store all the custom data of the font*/
static  lv_font_fmt_txt_glyph_cache_t cache;
#endif

#if LVGL_VERSION_MAJOR >= 8
static const lv_font_fmt_txt_dsc_t font_dsc = {
#else
static lv_font_fmt_txt_dsc_t font_dsc = {
#endif
    .glyph_bitmap = glyph_bitmap,
    .glyph_dsc = glyph_dsc,
    .cmaps = cmaps,
    .kern_dsc = NULL,
    .kern_scale = 0,
    .cmap_num = 5,
    .bpp = 1,
    .kern_classes = 0,
    .bitmap_format = 0,
#if LVGL_VERSION_MAJOR == 8
    .cache = &cache
#endif
};



/*-----------------
 *  PUBLIC FONT
 *----------------*/

/*Initialize a public general font descriptor*/
#if LVGL_VERSION_MAJOR >= 8
const lv_font_t ui_font_courier_new_40 = {
#else
lv_font_t ui_font_courier_new_40 = {
#endif
    .get_glyph_dsc = lv_font_get_glyph_dsc_fmt_txt,    /*Function pointer to get glyph's data*/
    .get_glyph_bitmap = lv_font_get_bitmap_fmt_txt,    /*Function pointer to get glyph's bitmap*/
    .line_height = 39,          /*The maximum line height required by the font*/
    .base_line = 11,             /*Baseline measured from the bottom of the line*/
#if !(LVGL_VERSION_MAJOR == 6 && LVGL_VERSION_MINOR == 0)
    .subpx = LV_FONT_SUBPX_NONE,
#endif
#if LV_VERSION_CHECK(7, 4, 0) || LVGL_VERSION_MAJOR >= 8
    .underline_position = -9,
    .underline_thickness = 2,
#endif
    .dsc = &font_dsc,          /*The custom font data. Will be accessed by `get_glyph_bitmap/dsc` */
#if LV_VERSION_CHECK(8, 2, 0) || LVGL_VERSION_MAJOR >= 9
    .fallback = NULL,
#endif
    .user_data = NULL,
};



#endif /*#if UI_FONT_COURIER_NEW_40*/
