yopocho/ChristmasMantelClock/src/ui/ui_font_courier_new_72.c

/*******************************************************************************
 * Size: 72 px
 * Bpp: 1
 * Opts: --bpp 1 --size 72 --no-compress --font ..\..\Downloads\cour.ttf --symbols 0123456789: --format lvgl
 ******************************************************************************/

#ifdef __has_include
    #if __has_include("lvgl.h")
        #ifndef LV_LVGL_H_INCLUDE_SIMPLE
            #define LV_LVGL_H_INCLUDE_SIMPLE
        #endif
    #endif
#endif

#ifdef LV_LVGL_H_INCLUDE_SIMPLE
    #include "lvgl.h"
#else
    #include "lvgl.h"
#endif

#ifndef UI_FONT_COURIER_NEW_72
#define UI_FONT_COURIER_NEW_72 1
#endif

#if UI_FONT_COURIER_NEW_72

/*-----------------
 *    BITMAPS
 *----------------*/

/*Store the image of the glyphs*/
static LV_ATTRIBUTE_LARGE_CONST const uint8_t glyph_bitmap[] = {
    /* U+0030 "0" */
    0x0, 0x3f, 0x80, 0x0, 0x1f, 0xfc, 0x0, 0xf,
    0xff, 0xe0, 0x3, 0xf0, 0x7e, 0x0, 0xf8, 0x3,
    0xe0, 0x1e, 0x0, 0x3c, 0x7, 0x80, 0x3, 0xc0,
    0xe0, 0x0, 0x38, 0x3c, 0x0, 0x7, 0x87, 0x0,
    0x0, 0x71, 0xe0, 0x0, 0xf, 0x38, 0x0, 0x0,
    0xe7, 0x0, 0x0, 0x1c, 0xe0, 0x0, 0x3, 0xbc,
    0x0, 0x0, 0x7f, 0x0, 0x0, 0x7, 0xe0, 0x0,
    0x0, 0xfc, 0x0, 0x0, 0x1f, 0x80, 0x0, 0x3,
    0xf0, 0x0, 0x0, 0x7e, 0x0, 0x0, 0xf, 0xc0,
    0x0, 0x1, 0xf8, 0x0, 0x0, 0x3f, 0x0, 0x0,
    0x7, 0xe0, 0x0, 0x0, 0xfc, 0x0, 0x0, 0x1f,
    0x80, 0x0, 0x3, 0xf0, 0x0, 0x0, 0x7e, 0x0,
    0x0, 0xf, 0xc0, 0x0, 0x1, 0xf8, 0x0, 0x0,
    0x3f, 0x0, 0x0, 0x7, 0xf0, 0x0, 0x1, 0xee,
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
    0xff, 0xfb, 0xfe, 0x1f, 0x0, 0x0, 0x0, 0x0,
    0x0, 0x0, 0x0, 0x0, 0x0, 0x0, 0x0, 0x0,
    0x0, 0x0, 0x0, 0x0, 0x0, 0x0, 0x0, 0x0,
    0xf8, 0x7f, 0xdf, 0xff, 0xff, 0xff, 0xff, 0xff,
    0xff, 0x9f, 0xf0, 0xf8
};


/*---------------------
 *  GLYPH DESCRIPTION
 *--------------------*/

static const lv_font_fmt_txt_glyph_dsc_t glyph_dsc[] = {
    {.bitmap_index = 0, .adv_w = 0, .box_w = 0, .box_h = 0, .ofs_x = 0, .ofs_y = 0} /* id = 0 reserved */,
    {.bitmap_index = 0, .adv_w = 691, .box_w = 27, .box_h = 47, .ofs_x = 8, .ofs_y = -1},
    {.bitmap_index = 159, .adv_w = 691, .box_w = 27, .box_h = 45, .ofs_x = 8, .ofs_y = 0},
    {.bitmap_index = 311, .adv_w = 691, .box_w = 29, .box_h = 46, .ofs_x = 6, .ofs_y = 0},
    {.bitmap_index = 478, .adv_w = 691, .box_w = 30, .box_h = 47, .ofs_x = 6, .ofs_y = -1},
    {.bitmap_index = 655, .adv_w = 691, .box_w = 27, .box_h = 45, .ofs_x = 8, .ofs_y = 0},
    {.bitmap_index = 807, .adv_w = 691, .box_w = 30, .box_h = 46, .ofs_x = 6, .ofs_y = -1},
    {.bitmap_index = 980, .adv_w = 691, .box_w = 27, .box_h = 47, .ofs_x = 10, .ofs_y = -1},
    {.bitmap_index = 1139, .adv_w = 691, .box_w = 27, .box_h = 45, .ofs_x = 7, .ofs_y = 0},
    {.bitmap_index = 1291, .adv_w = 691, .box_w = 27, .box_h = 47, .ofs_x = 8, .ofs_y = -1},
    {.bitmap_index = 1450, .adv_w = 691, .box_w = 27, .box_h = 47, .ofs_x = 10, .ofs_y = -1},
    {.bitmap_index = 1609, .adv_w = 691, .box_w = 11, .box_h = 32, .ofs_x = 16, .ofs_y = -1}
};

/*---------------------
 *  CHARACTER MAPPING
 *--------------------*/



/*Collect the unicode lists and glyph_id offsets*/
static const lv_font_fmt_txt_cmap_t cmaps[] =
{
    {
        .range_start = 48, .range_length = 11, .glyph_id_start = 1,
        .unicode_list = NULL, .glyph_id_ofs_list = NULL, .list_length = 0, .type = LV_FONT_FMT_TXT_CMAP_FORMAT0_TINY
    }
};



/*--------------------
 *  ALL CUSTOM DATA
 *--------------------*/

#if LVGL_VERSION_MAJOR == 8
/*Store all the custom data of the font*/
static  lv_font_fmt_txt_glyph_cache_t cache;
#endif

#if LVGL_VERSION_MAJOR >= 8
static const lv_font_fmt_txt_dsc_t font_dsc = {
#else
static lv_font_fmt_txt_dsc_t font_dsc = {
#endif
    .glyph_bitmap = glyph_bitmap,
    .glyph_dsc = glyph_dsc,
    .cmaps = cmaps,
    .kern_dsc = NULL,
    .kern_scale = 0,
    .cmap_num = 1,
    .bpp = 1,
    .kern_classes = 0,
    .bitmap_format = 0,
#if LVGL_VERSION_MAJOR == 8
    .cache = &cache
#endif
};



/*-----------------
 *  PUBLIC FONT
 *----------------*/

/*Initialize a public general font descriptor*/
#if LVGL_VERSION_MAJOR >= 8
const lv_font_t ui_font_courier_new_72 = {
#else
lv_font_t ui_font_courier_new_72 = {
#endif
    .get_glyph_dsc = lv_font_get_glyph_dsc_fmt_txt,    /*Function pointer to get glyph's data*/
    .get_glyph_bitmap = lv_font_get_bitmap_fmt_txt,    /*Function pointer to get glyph's bitmap*/
    .line_height = 47,          /*The maximum line height required by the font*/
    .base_line = 1,             /*Baseline measured from the bottom of the line*/
#if !(LVGL_VERSION_MAJOR == 6 && LVGL_VERSION_MINOR == 0)
    .subpx = LV_FONT_SUBPX_NONE,
#endif
#if LV_VERSION_CHECK(7, 4, 0) || LVGL_VERSION_MAJOR >= 8
    .underline_position = -17,
    .underline_thickness = 3,
#endif
    .dsc = &font_dsc,          /*The custom font data. Will be accessed by `get_glyph_bitmap/dsc` */
#if LV_VERSION_CHECK(8, 2, 0) || LVGL_VERSION_MAJOR >= 9
    .fallback = NULL,
#endif
    .user_data = NULL,
};



#endif /*#if UI_FONT_COURIER_NEW_72*/
