yopocho/ChristmasMantelClock/src/ui/styles.h

#ifndef EEZ_LVGL_UI_STYLES_H
#define EEZ_LVGL_UI_STYLES_H

#include <lvgl.h>

#ifdef __cplusplus
extern "C" {
#endif

// Style: style_buttons_digital_clock_set_time
lv_style_t *get_style_style_buttons_digital_clock_set_time_MAIN_DEFAULT();
lv_style_t *get_style_style_buttons_digital_clock_set_time_MAIN_FOCUS_KEY();
void add_style_style_buttons_digital_clock_set_time(lv_obj_t *obj);
void remove_style_style_buttons_digital_clock_set_time(lv_obj_t *obj);

// Style: style_spinboxes_digital_clock
lv_style_t *get_style_style_spinboxes_digital_clock_MAIN_DEFAULT();
lv_style_t *get_style_style_spinboxes_digital_clock_MAIN_FOCUS_KEY();
lv_style_t *get_style_style_spinboxes_digital_clock_CURSOR_DEFAULT();
void add_style_style_spinboxes_digital_clock(lv_obj_t *obj);
void remove_style_style_spinboxes_digital_clock(lv_obj_t *obj);

// Style: style_labels_digital_clock
lv_style_t *get_style_style_labels_digital_clock_MAIN_DEFAULT();
void add_style_style_labels_digital_clock(lv_obj_t *obj);
void remove_style_style_labels_digital_clock(lv_obj_t *obj);

// Style: style_labels_menu
lv_style_t *get_style_style_labels_menu_MAIN_DEFAULT();
void add_style_style_labels_menu(lv_obj_t *obj);
void remove_style_style_labels_menu(lv_obj_t *obj);

// Style: style_spinboxes_menu
lv_style_t *get_style_style_spinboxes_menu_MAIN_DEFAULT();
lv_style_t *get_style_style_spinboxes_menu_MAIN_FOCUS_KEY();
lv_style_t *get_style_style_spinboxes_menu_CURSOR_DEFAULT();
lv_style_t *get_style_style_spinboxes_menu_SELECTED_DEFAULT();
void add_style_style_spinboxes_menu(lv_obj_t *obj);
void remove_style_style_spinboxes_menu(lv_obj_t *obj);

// Style: style_buttons_menu
lv_style_t *get_style_style_buttons_menu_MAIN_FOCUS_KEY();
lv_style_t *get_style_style_buttons_menu_MAIN_DEFAULT();
void add_style_style_buttons_menu(lv_obj_t *obj);
void remove_style_style_buttons_menu(lv_obj_t *obj);

// Style: style_scale_analog_clock
lv_style_t *get_style_style_scale_analog_clock_MAIN_DEFAULT();
lv_style_t *get_style_style_scale_analog_clock_INDICATOR_DEFAULT();
lv_style_t *get_style_style_scale_analog_clock_ITEMS_DEFAULT();
void add_style_style_scale_analog_clock(lv_obj_t *obj);
void remove_style_style_scale_analog_clock(lv_obj_t *obj);

// Style: style_rollers_menu
lv_style_t *get_style_style_rollers_menu_MAIN_DEFAULT();
lv_style_t *get_style_style_rollers_menu_MAIN_FOCUS_KEY();
lv_style_t *get_style_style_rollers_menu_SELECTED_DEFAULT();
void add_style_style_rollers_menu(lv_obj_t *obj);
void remove_style_style_rollers_menu(lv_obj_t *obj);

// Style: style_labels_analog_clock
lv_style_t *get_style_style_labels_analog_clock_MAIN_DEFAULT();
void add_style_style_labels_analog_clock(lv_obj_t *obj);
void remove_style_style_labels_analog_clock(lv_obj_t *obj);

// Style: style_led_analog_clock
lv_style_t *get_style_style_led_analog_clock_MAIN_DEFAULT();
void add_style_style_led_analog_clock(lv_obj_t *obj);
void remove_style_style_led_analog_clock(lv_obj_t *obj);

// Style: style_line_hr_analog_clock
lv_style_t *get_style_style_line_hr_analog_clock_MAIN_DEFAULT();
void add_style_style_line_hr_analog_clock(lv_obj_t *obj);
void remove_style_style_line_hr_analog_clock(lv_obj_t *obj);

// Style: style_line_min_analog_clock
lv_style_t *get_style_style_line_min_analog_clock_MAIN_DEFAULT();
void add_style_style_line_min_analog_clock(lv_obj_t *obj);
void remove_style_style_line_min_analog_clock(lv_obj_t *obj);



#ifdef __cplusplus
}
#endif

#endif /*EEZ_LVGL_UI_STYLES_H*/
